rosco-m68k/rosco_m68k/code/firmware/attic/rhombus-monitor/README.md

# Machine-monitor from Rhombus 

This is the machine monitor from Rhombus (http://github.com/zenmetsu/rhombus) ported to run on the rosco_m68k.

Porting required fairly minimal effort (changes to the memory layout, changing the MFP initialisation to suit
my clocks and changing of a couple of address modes here and there due to the original being designed for
the 68020).

The main driving force behind porting this was as a sanity check while trying to debug the serial receiver.
I figured if this also didn't work then it would at least eliminate my own code as the reason the receiver
didn't work.

~It didn't (and as of today, doesn't) work. So it seems the problem is most likely a hardware issue.~ 
EDIT: Input is now working. The issue was found to be a faulty MC68901 IC - after replacing that it immediately worked. The monitor itself however does not work, instead it causes an illegal instruction on entry of any valid command. I suspect there is stll something MC68020-specific in here that VASM isn't picking up even with the -m68010 flag.

This code remains the property of it's original author(s) and is subject to the original license.
The original README is reproduced below in its entirity.

# rhombus

A minimal m68k system utilizing the 68020 microprocessor 

Project page located here: https://hackaday.io/project/8725-rhombus

Building upon the Motorola Application Note 1015 which can be found at the following address:
http://archive.retro.co.za/archive/computers/AppNotes/Motorola-AN1015.pdf

So far, there have been several typos which have been corrected within the original Motorola code, 
as well as one hardware fault in the included schematic.
As of https://github.com/zenmetsu/rhombus/commit/a4d3d180cdeede65c75aaab68ca234bd8a448fac   the code
is functional and will boot up to produce serial output.

The schematic within the application note is correct to the best of my knowledge with the exception
that on the MC68901, the TCO output must be tied externally to RC, and TDO needs to be tied to TC.
The provided schematic omitted these connections and the documentation for the multi-function peripheral
leaves much to be desired, leading one to suspect that the clock could be passed internally 
via configuration.

The system board currently consists of CPU, RAM, ROM, an MC68901 multifunction peripheral, and a Xilinx XC95108 CPLD.

RAM sizing and error checking is in place.  Monitor has the ability to analyze or change memory contents.
Secondary monitor written to expand functionality.  Register viewing/modification possible, as is vectored
selection of input/output devices.  Added NMI exception handler and trace/breakpoint functionality.

Second monitor now contains all of the functionality of the original.  I am currently attempting to migrate the system to a VME style bus, however I am debating using a standard VME bus with a non-standard 4x32 pin header.  The issue revolves around the feasibility of such a design due to the need for boards with more than 2 layers.

## Building

monitor.x68 can be assembled with vasm using the following command :

`vasmm68k_mot -m68020 -Fbin ./monitor.x68 -o monitor.bin`

The resulting binary can be loaded onto a ROM for booting.

## Additional programs
### mandelbrot - An ASCII Mandelbrot fractal explorer

mandelbrot.x68 can be assembled in the same manner as the monitor.  The resulting binary can be put into human readable format for pasting into the monitor with the following:

`xxd -u -s +15732736 -l 600 mandelbrot.bin | sed -e 's/  .*//' -e 's/^.*://' | sed -e :a -e '$!N; s/\n//; ta'`

Simply copy the code (including the leading space before the first long word) and, on the monitor, enter the command `MEM F01000`

After hitting Enter, paste the code and it should be placed into RAM.  When paste is done, hit Enter to exit memory write mode and execute the program with `JUMP F01000`

Keys are as follows:
```
W,A,S,D   PAN up/left/down/right
Q,E       ZOOM out/in
Z,C       ITERATION decrease,increase
R         RESETS to original conditions
X         EXITS to ROM monitor
```

## Next steps:

- S-Record load over serial
- Addition of an MC68681 DUART which will work as auxillary serial port as well as keyboard input
- Addition of FT245 USB FIFO for auxillary serial connection
- Increasing RAM data bus to 32bits.  ROM to remain 8bit due to simplicity of flashing devices.
- Floppy drive interface
- PS/2 Keyboard via intel N8042 microcontroller

Currently rebuilding CPLD files due to loss of CPLD project files
