rosco-m68k/rosco_m68k/code/software/lcd-ili9341/images/colorcube.bmp

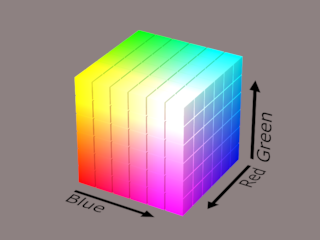
code/software/lcd-ili9341/images/colorcube.bmp
