rosco-m68k/rosco_m68k/code/software/lcd-ili9341/images/rosco_web.bmp

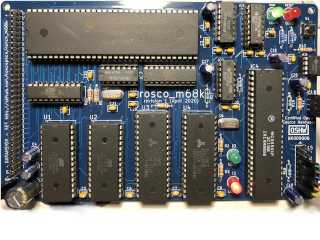
code/software/lcd-ili9341/images/rosco_web.bmp
