rosco-m68k/rosco_m68k/images/4077381582746008339.jpg

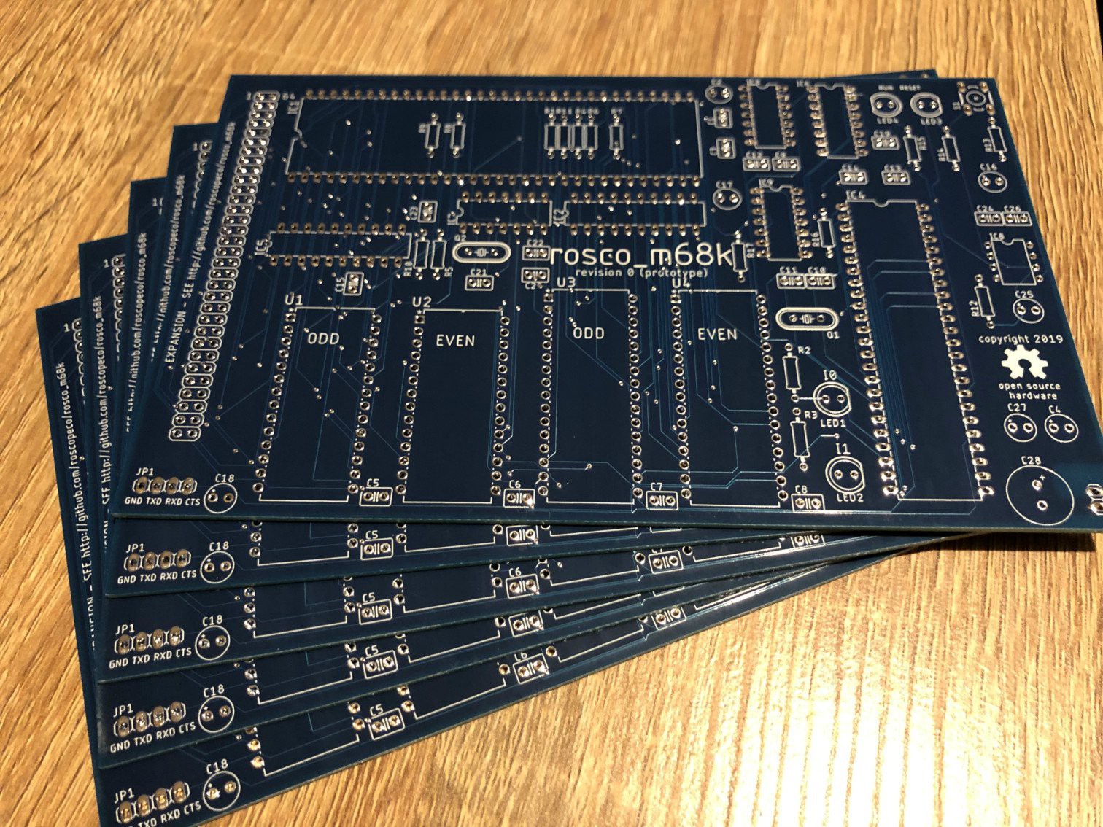
images/4077381582746008339.jpg
