rosco-m68k/rosco_m68k/images/bus_access_on_reset.png

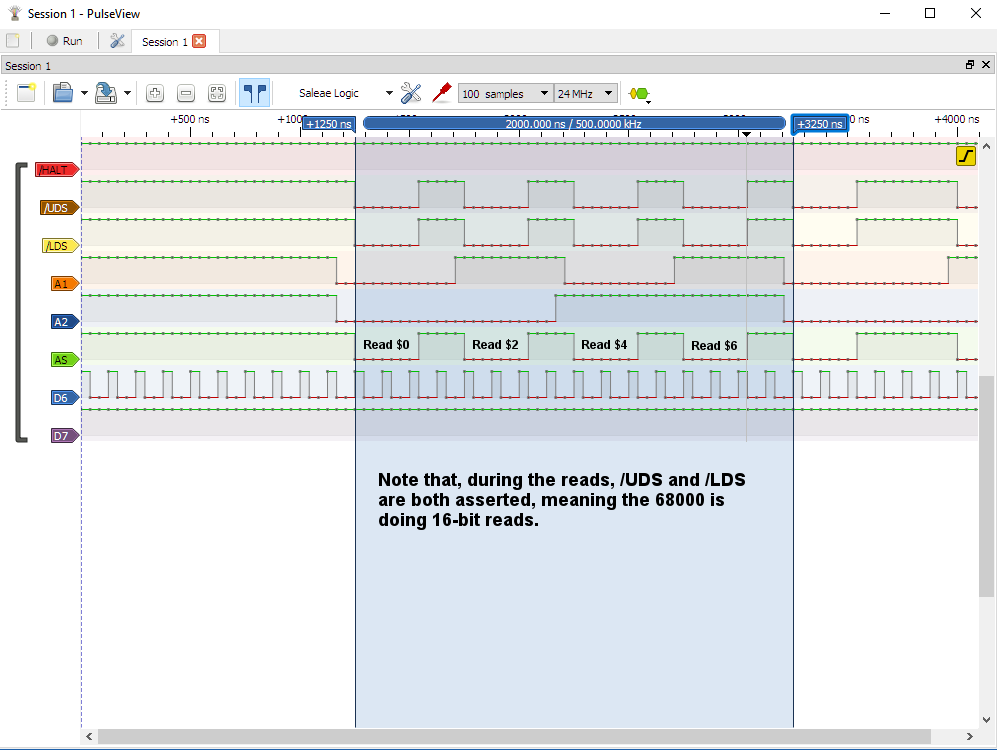
images/bus_access_on_reset.png
