rosco-m68k/rosco_m68k/images/pcb_r1.png

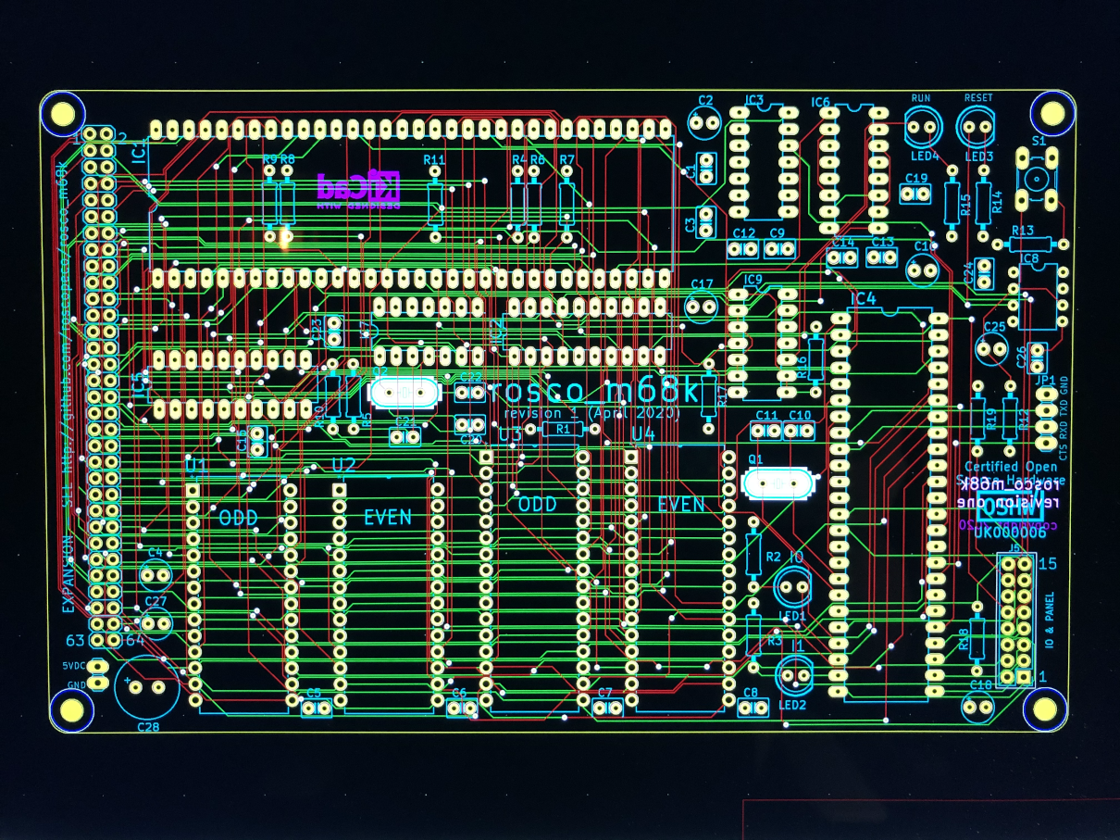
images/pcb_r1.png
