rosco-m68k/rosco_m68k/design/EAGLE/address_decoder_v2.sch

## EAGLE design design/EAGLE/address_decoder_v2.sch (2019-07-15)

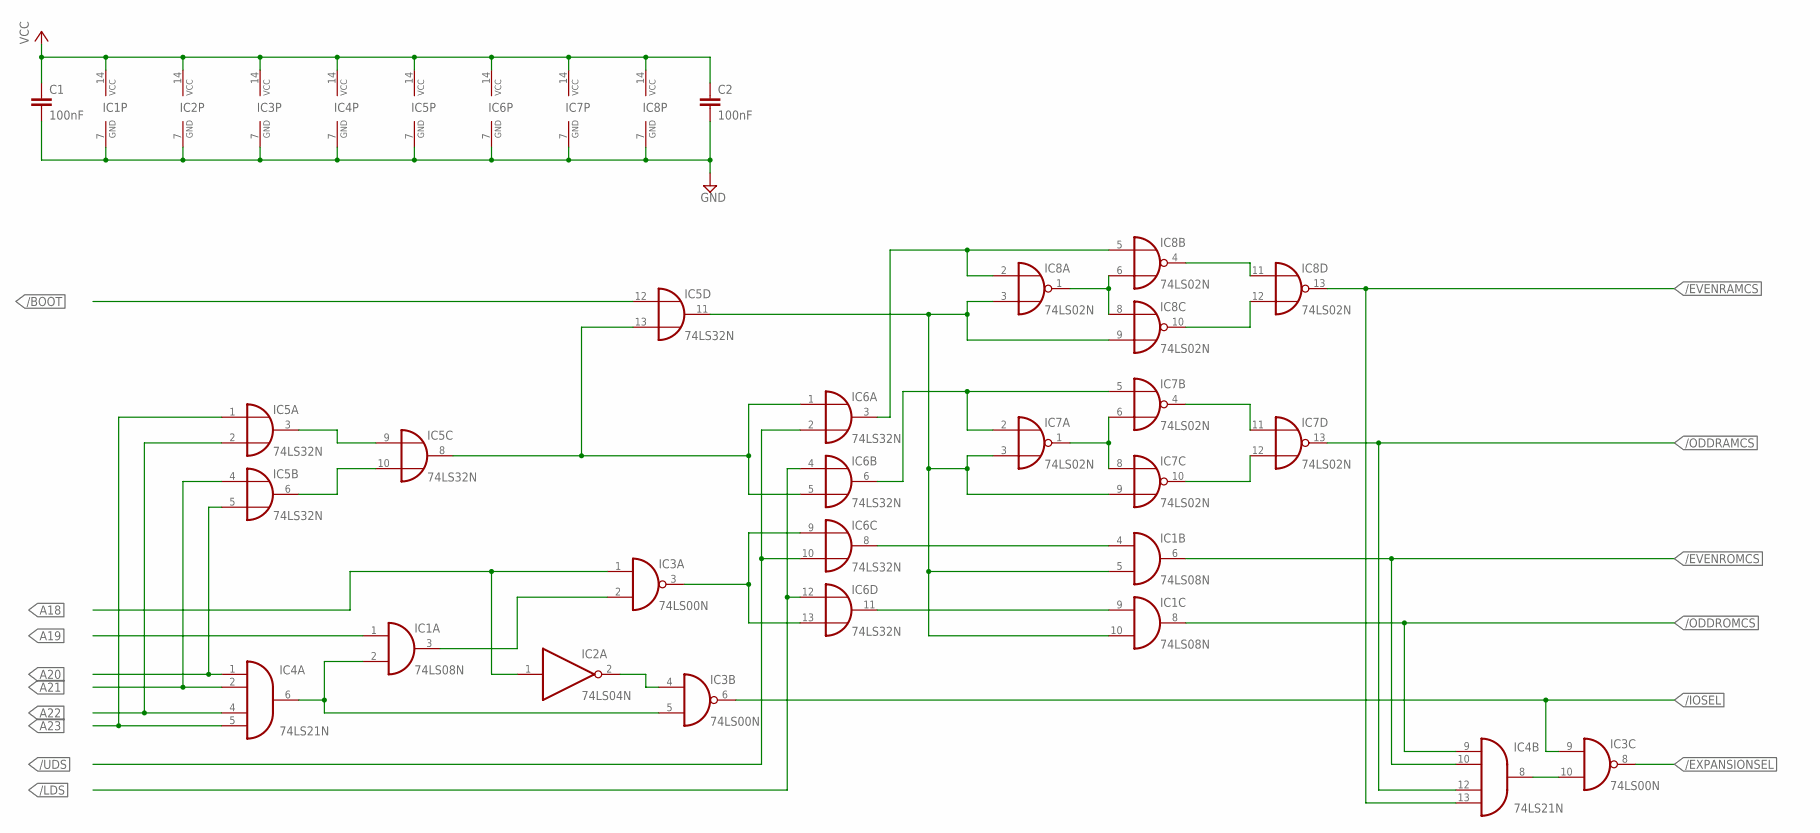
[picture p56: schematic address_decoder_v2.sch, sheet 1]

Parts:
C1, C2: 100nF; C025-024X044
IC1: 74LS08N; DIL14
IC2: 74LS04N; DIL14
IC3: 74LS00N; DIL14
IC4: 74LS21N; DIL14
IC5, IC6: 74LS32N; DIL14
IC7, IC8: 74LS02N; DIL14

Connections:
/BOOT: IC5.12 (I0)
/EVENRAMCS: IC4.13 (I3), IC8.13 (O)
/EVENROMCS: IC1.6 (O), IC4.10 (I1)
/EXPANSIONSEL: IC3.8 (O)
/IOSEL: IC3.6 (O), IC3.9 (I0)
/LDS: IC6.4 (I0), IC6.12 (I0)
/ODDRAMCS: IC4.12 (I2), IC7.13 (O)
/ODDROMCS: IC1.8 (O), IC4.9 (I0)
/UDS: IC6.2 (I1), IC6.10 (I1)
A18: IC2.1 (I), IC3.1 (I0)
A19: IC1.1 (I0)
A20: IC4.1 (I0), IC5.5 (I1)
A21: IC4.2 (I1), IC5.4 (I0)
A22: IC4.4 (I2), IC5.2 (I1)
A23: IC4.5 (I3), IC5.1 (I0)
GND: C1.2, C2.2, IC1.7 (GND), IC2.7 (GND), IC3.7 (GND), IC4.7 (GND), IC5.7 (GND), IC6.7 (GND), IC7.7 (GND), IC8.7 (GND)
unnamed: IC8.1 (O), IC8.6 (I1), IC8.8 (I0)
unnamed: IC8.4 (O), IC8.11 (I0)
unnamed: IC8.10 (O), IC8.12 (I1)
unnamed: IC6.3 (O), IC8.2 (I0), IC8.5 (I0)
unnamed: IC3.10 (I1), IC4.8 (O)
unnamed: IC7.1 (O), IC7.6 (I1), IC7.8 (I0)
unnamed: IC7.4 (O), IC7.11 (I0)
unnamed: IC6.6 (O), IC7.2 (I0), IC7.5 (I0)
unnamed: IC1.5 (I1), IC1.10 (I1), IC5.11 (O), IC7.3 (I1), IC7.9 (I1), IC8.3 (I1), IC8.9 (I1)
unnamed: IC7.10 (O), IC7.12 (I1)
unnamed: IC1.4 (I0), IC6.8 (O)
unnamed: IC1.9 (I0), IC6.11 (O)
unnamed: IC5.3 (O), IC5.9 (I0)
unnamed: IC5.6 (O), IC5.10 (I1)
unnamed: IC3.3 (O), IC6.9 (I0), IC6.13 (I1)
unnamed: IC1.2 (I1), IC3.5 (I1), IC4.6 (O)
unnamed: IC2.2 (O), IC3.4 (I0)
unnamed: IC5.8 (O), IC5.13 (I1), IC6.1 (I0), IC6.5 (I1)
unnamed: IC1.3 (O), IC3.2 (I1)
VCC: C1.1, C2.1, IC1.14 (VCC), IC2.14 (VCC), IC3.14 (VCC), IC4.14 (VCC), IC5.14 (VCC), IC6.14 (VCC), IC7.14 (VCC), IC8.14 (VCC)

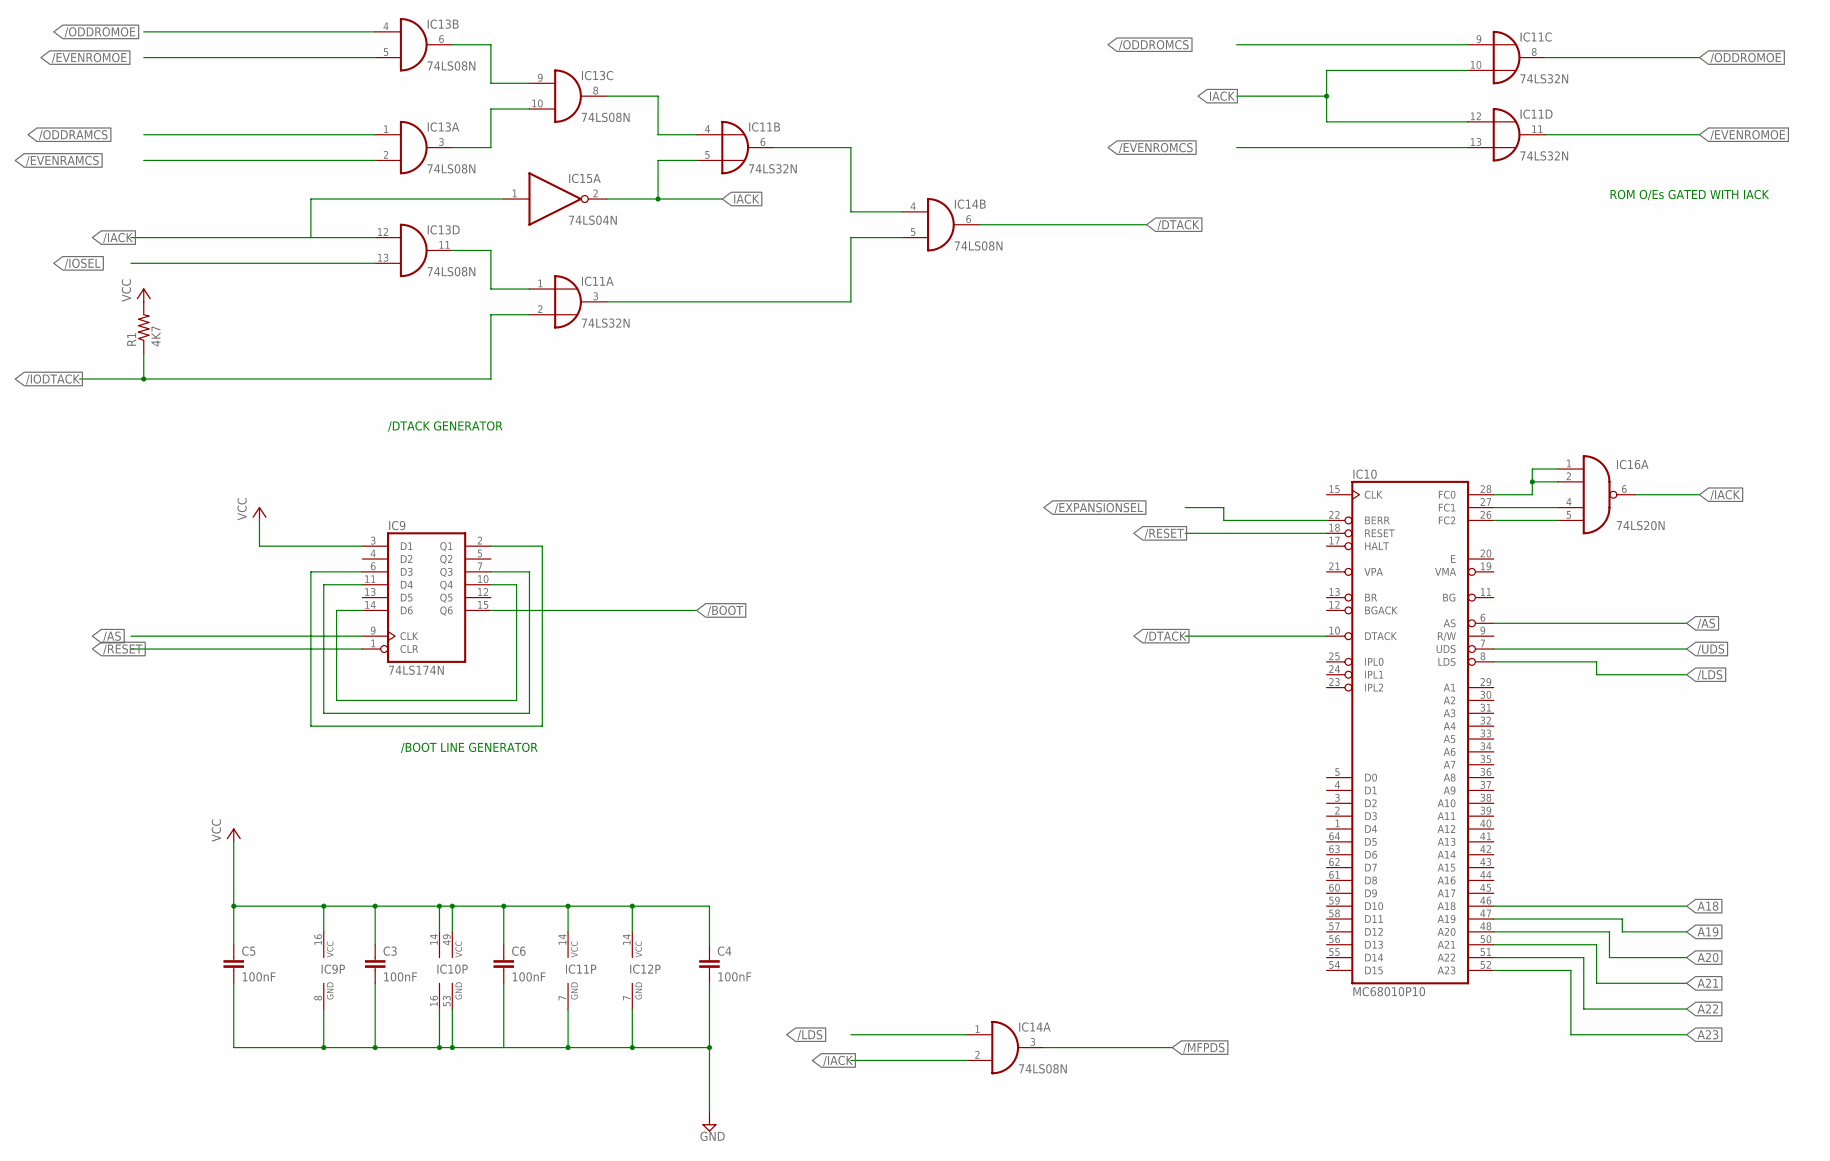
[picture p57: schematic address_decoder_v2.sch, sheet 2]

Parts:
C3, C4, C5, C6: 100nF; C5B3
IC9: 74LS174N; DIL16
IC10: MC68010P10; DIL64
IC11: 74LS32N; DIL14
IC12: 74LS21N; DIL14
IC13, IC14: 74LS08N; DIL14
IC15: 74LS04N; DIL14
IC16: 74LS20N; DIL14
R1: 4K7; 0204/7

Connections:
/AS: IC9.9 (CLK), IC10.6 (AS)
/BOOT: IC9.15 (Q6)
/DTACK: IC10.10 (DTACK), IC14.6 (O)
/EVENRAMCS: IC13.2 (I1)
/EVENROMCS: IC11.13 (I1)
/EVENROMOE: IC11.11 (O), IC13.5 (I1)
/EXPANSIONSEL: IC10.22 (BERR)
/IACK: IC13.12 (I0), IC14.2 (I1), IC15.1 (I), IC16.6 (O)
/IODTACK: IC11.2 (I1), R1.1
/IOSEL: IC13.13 (I1)
/LDS: IC10.8 (LDS), IC14.1 (I0)
/MFPDS: IC14.3 (O)
/ODDRAMCS: IC13.1 (I0)
/ODDROMCS: IC11.9 (I0)
/ODDROMOE: IC11.8 (O), IC13.4 (I0)
/RESET: IC9.1 (CLR), IC10.18 (RESET)
/UDS: IC10.7 (UDS)
A18: IC10.46 (A18)
A19: IC10.47 (A19)
A20: IC10.48 (A20)
A21: IC10.50 (A21)
A22: IC10.51 (A22)
A23: IC10.52 (A23)
GND: C3.2, C4.2, C5.2, IC9.8 (GND), IC10.16 (GND), IC10.53 (GND), IC11.7 (GND), IC12.7 (GND)
GND1: C6.2
IACK: IC11.5 (I1), IC11.10 (I1), IC11.12 (I0), IC15.2 (O)
unnamed: IC13.6 (O), IC13.9 (I0)
unnamed: IC9.7 (Q3), IC9.11 (D4)
unnamed: IC9.10 (Q4), IC9.14 (D6)
unnamed: IC9.2 (Q1), IC9.6 (D3)
unnamed: IC13.3 (O), IC13.10 (I1)
unnamed: IC11.4 (I0), IC13.8 (O)
unnamed: IC11.1 (I0), IC13.11 (O)
unnamed: IC11.6 (O), IC14.4 (I0)
unnamed: IC11.3 (O), IC14.5 (I1)
unnamed: IC10.26 (FC2), IC16.5 (I3)
unnamed: IC10.27 (FC1), IC16.4 (I2)
unnamed: IC10.28 (FC0), IC16.1 (I0), IC16.2 (I1)
VCC: C3.1, C4.1, C5.1, C6.1, IC9.3 (D1), IC9.16 (VCC), IC10.14 (VCC), IC10.49 (VCC), IC11.14 (VCC), IC12.14 (VCC), R1.2

Notes on the sheet:
/BOOT LINE GENERATOR
/DTACK GENERATOR
ROM O/Es GATED WITH IACK
