rosco-m68k/rosco_m68k/design/EAGLE/clock.sch

## EAGLE design design/EAGLE/clock.sch (2019-03-28)

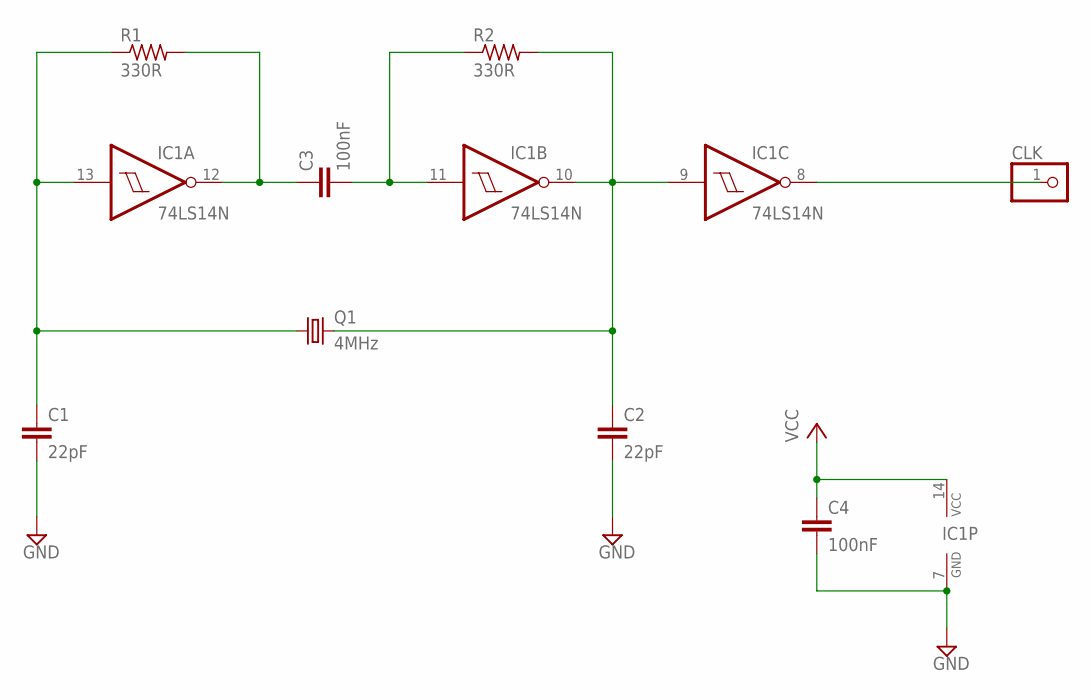
[picture p59: schematic clock.sch]

Parts:
C1, C2: 22pF; C025-025X050
C3, C4: 100nF; C025-025X050
CLK: PINHD-1X1; 1X01
IC1: 74LS14N; DIL14
Q1: 4MHz; HC49/S
R1, R2: 330R; 0207/10

Connections:
GND: C1.2, C2.2, C4.2, IC1.7 (GND)
unnamed: C3.1, IC1.12 (O), R1.2
unnamed: C3.2, IC1.11 (I), R2.1
unnamed: C2.1, IC1.9 (I), IC1.10 (O), Q1.2, R2.2
unnamed: C1.1, IC1.13 (I), Q1.1, R1.1
unnamed: CLK.1, IC1.8 (O)
VCC: C4.1, IC1.14 (VCC)
