rosco-m68k/rosco_m68k/design/EAGLE/dtack-generator.sch

## EAGLE design design/EAGLE/dtack-generator.sch (2019-05-19)

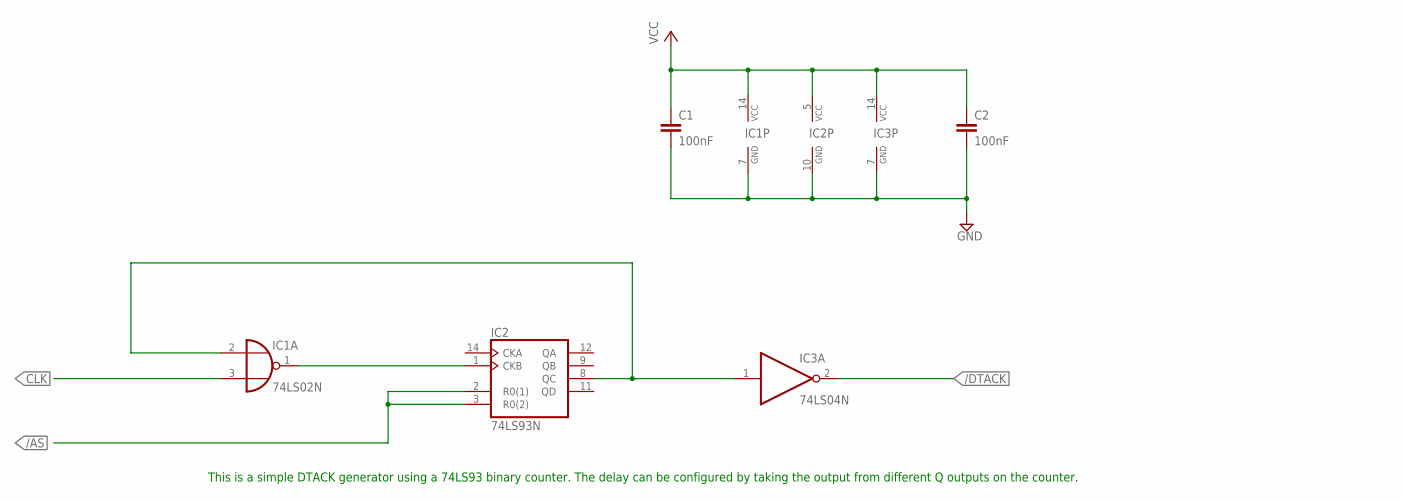
[picture p60: schematic dtack-generator.sch]

Parts:
C1, C2: 100nF; C025-024X044
IC1: 74LS02N; DIL14
IC2: 74LS93N; DIL14
IC3: 74LS04N; DIL14

Connections:
/AS: IC2.2 (R0(1)), IC2.3 (R0(2))
/DTACK: IC3.2 (O)
CLK: IC1.3 (I1)
GND: C1.2, C2.2, IC1.7 (GND), IC2.10 (GND), IC3.7 (GND)
unnamed: IC1.1 (O), IC2.1 (CKB)
unnamed: IC1.2 (I0), IC2.8 (QC), IC3.1 (I)
VCC: C1.1, C2.1, IC1.14 (VCC), IC2.5 (VCC), IC3.14 (VCC)

Notes on the sheet:
This is a simple DTACK generator using a 74LS93 binary counter. The delay can be configured by taking the output from different Q outputs on the counter.
