rosco-m68k/rosco_m68k/design/EAGLE/m68k_free_run.sch

## EAGLE design design/EAGLE/m68k_free_run.sch (2019-04-28)

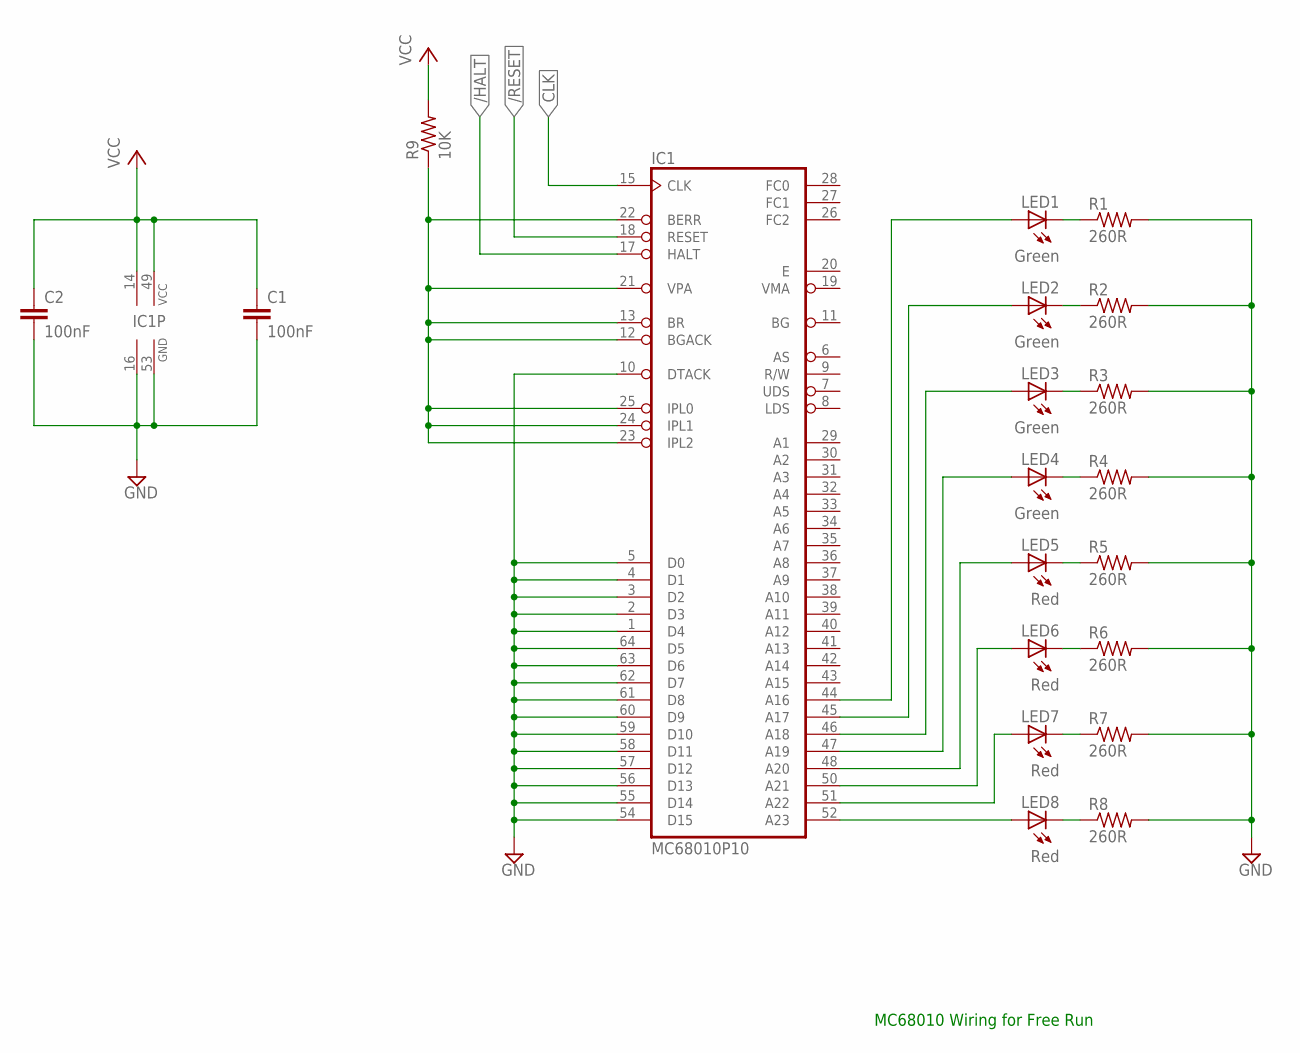
[picture p61: schematic m68k_free_run.sch]

Parts:
C1, C2: 100nF; C025-024X044
IC1: MC68010P10; DIL64
LED1, LED2, LED3, LED4: Green; LED5MM
LED5, LED6, LED7, LED8: Red; LED5MM
R1, R2, R3, R4, R5, R6, R7, R8: 260R; 0207/10
R9: 10K; 0207/10

Connections:
/HALT: IC1.17 (HALT)
/RESET: IC1.18 (RESET)
CLK: IC1.15 (CLK)
GND: C1.2, C2.2, IC1.1 (D4), IC1.2 (D3), IC1.3 (D2), IC1.4 (D1), IC1.5 (D0), IC1.10 (DTACK), IC1.16 (GND), IC1.53 (GND), IC1.54 (D15), IC1.55 (D14), IC1.56 (D13), IC1.57 (D12), IC1.58 (D11), IC1.59 (D10), IC1.60 (D9), IC1.61 (D8), IC1.62 (D7), IC1.63 (D6), IC1.64 (D5), R1.2, R2.2, R3.2, R4.2, R5.2, R6.2, R7.2, R8.2
unnamed: IC1.52 (A23), LED8.A
unnamed: IC1.51 (A22), LED7.A
unnamed: IC1.50 (A21), LED6.A
unnamed: IC1.48 (A20), LED5.A
unnamed: IC1.47 (A19), LED4.A
unnamed: IC1.46 (A18), LED3.A
unnamed: IC1.45 (A17), LED2.A
unnamed: IC1.44 (A16), LED1.A
unnamed: LED1.K (C), R1.1
unnamed: LED2.K (C), R2.1
unnamed: LED3.K (C), R3.1
unnamed: LED4.K (C), R4.1
unnamed: LED5.K (C), R5.1
unnamed: LED6.K (C), R6.1
unnamed: LED7.K (C), R7.1
unnamed: LED8.K (C), R8.1
unnamed: IC1.12 (BGACK), IC1.13 (BR), IC1.21 (VPA), IC1.22 (BERR), IC1.23 (IPL2), IC1.24 (IPL1), IC1.25 (IPL0), R9.1
VCC: C1.1, C2.1, IC1.14 (VCC), IC1.49 (VCC), R9.2

Notes on the sheet:
MC68010 Wiring for Free Run
