rosco-m68k/rosco_m68k/design/EAGLE/reset_circuit.sch

## EAGLE design design/EAGLE/reset_circuit.sch (2019-06-25)

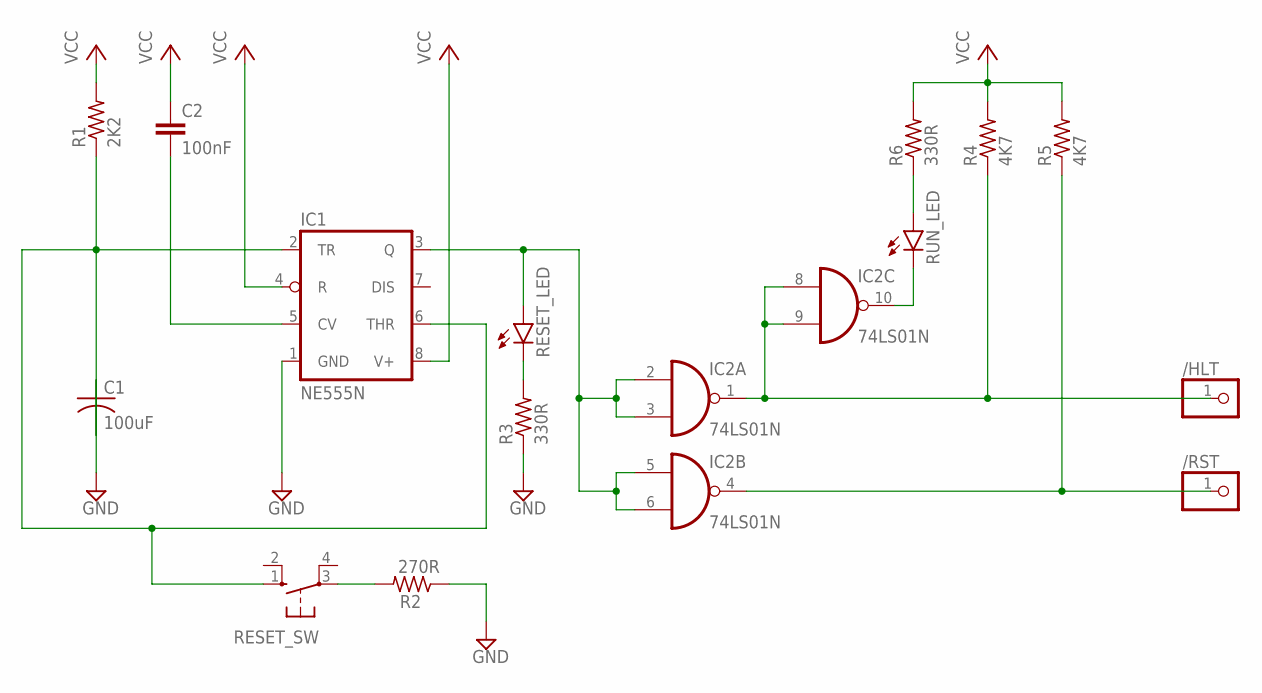
[picture p62: schematic reset_circuit.sch]

Parts:
/HLT: PINHD-1X1; 1X01
/RST: PINHD-1X1; 1X01
C1: 100uF; C025-025X050
C2: 100nF; C2.5-3
IC1: NE555N; DIL08
IC2: 74LS01N; DIL14
R1: 2K2; 0204/7
R2: 270R; 0204/7
R3, R6: 330R; 0204/7
R4, R5: 4K7; 0204/7
RESET_LED: LED5MM
RESET_SW: 10-XX; B3F-10XX
RUN_LED: LED5MM

Connections:
GND: C1.1, IC1.1 (GND), R2.1, R3.1
unnamed: C1.2, IC1.2 (TR), IC1.6 (THR), R1.1, RESET_SW.1 (S)
unnamed: C2.2, IC1.5 (CV)
unnamed: IC1.3 (Q), IC2.2 (I0), IC2.3 (I1), IC2.5 (I0), IC2.6 (I1), RESET_LED.A
unnamed: R3.2, RESET_LED.K (C)
unnamed: /HLT.1, IC2.1 (O), IC2.8 (I0), IC2.9 (I1), R4.1
unnamed: /RST.1, IC2.4 (O), R5.1
unnamed: IC2.10 (O), RUN_LED.K (C)
unnamed: R6.1, RUN_LED.A
unnamed: R2.2, RESET_SW.3
VCC: C2.1, IC1.4 (R), IC1.8 (V+), R1.2, R4.2, R5.2, R6.2
