rosco-m68k/rosco_m68k/design/r1.2/kicad/Cpu_Ram_Rom.sch

## KiCad design design/r1.2/kicad/Cpu_Ram_Rom.sch (2021-04-14)

Schematic: Cpu_Ram_Rom.sch

Parts:
C1, C2: 33pF; C2.5-3
C5, C6, C7, C8: 100nF; C2.5-3
IC1: MC68010P10; DIL64
IC4: MC68901P; DIL48
J2: Conn_01x06; 1X06
JP1: FTDI POWER; 1X02
LED1: GREEN; LED5MM
LED2: RED; LED5MM
Q1: 3.6864MHz; HC49_S
R1, R2: 330R; 0207_10
U1, U2: AT28C256-15PU; DIP-28_W15.24mm_LongPads
U3, U4: AS6C4008-55PCN; DIP-32_W15.24mm_LongPads

Notes on the sheet:
ODD
EVEN
MC68901
MC68010P10
AT28C64B or AT28C256
