rosco-m68k/rosco_m68k/design/r1.2/kicad/Glue.sch

## KiCad design design/r1.2/kicad/Glue.sch (2021-04-14)

Schematic: Glue.sch

Parts:
C7, C8, C9, C12, C13, C26: 100nF; C2.5-3
C25: 100uF; E2,5-5
IC2, IC3, IC5: ATF16V8BQL-15PU; DIL20
IC6: 74174N; DIP-16_W7.62mm_Socket_LongPads
IC7: 74LS93; DIP-14_W7.62mm_Socket_LongPads
IC8: 555N; DIP-8_W7.62mm_LongPads
IC9: 74LS01N; DIP-14_W7.62mm_Socket_LongPads
LED3: RED; LED5MM
LED4: GREEN; LED5MM
Q2: 5H8ET-10.000; Oscillator_DIP-8
Q3: 5H8ET-4.000; Oscillator_DIP-8
R3, R4, R6, R7, R8, R9, R11, R16, R17: 4K7; 0207_10
R12, R21: 2K2; 0207_10
R13: 270R; 0207_10
R14, R15: 330R; 0207_10
S1: 10-XX; B3F-10XX

Notes on the sheet:
RESET CIRCUIT
GLUE_LOGIC.PLD
/BOOT LINE GENERATOR
ADDRESS_DECODER.PLD
MFPSEL.PLD
DTACK WATCHDOG
