rosco-m68k/rosco_m68k/design/r1/kicad/Clock_Reset.sch

## KiCad design design/r1/kicad/Clock_Reset.sch (2020-05-26)

Schematic: Clock_Reset.sch

Parts:
C20, C22: 22pF; C2.5-3
C21, C23, C24, C26: 100nF; C2.5-3
C25, C27: 100uF; E2,5-5
C28: 470uF; E3,5-10
IC7: 7404N; DIL14
IC8: 555N; DIL08
IC9: 74LS01N; DIL14
JP2: PWR; 1X02
LED3: RED; LED5MM
LED4: GREEN; LED5MM
Q2: 8MHz; HC49_S
R4, R6, R7, R8, R9, R11, R16, R17: 4K7; 0207_10
R5, R10, R15: 1K2; 0207_10
R12: 2K2; 0207_10
R13: 270R; 0207_10
R14: 330R; 0207_10
S1: 10-XX; B3F-10XX

Notes on the sheet:
RESET CIRCUIT
SYSTEM CLOCK CIRCUIT
