rosco-m68k/rosco_m68k/design/r1/kicad/Dtack_Boot.sch

## KiCad design design/r1/kicad/Dtack_Boot.sch (2020-03-29)

Schematic: Dtack_Boot.sch

Parts:
C15, C19: 100nF; C2.5-3
C16, C17, C18: 100uF; E2,5-5
IC5: ATF16V8BQL; DIL20
IC6: 74174N; DIL16

Notes on the sheet:
/BOOT LINE GENERATOR
GLUE_LOGIC.PLD
