rosco-m68k/rosco_m68k/design/r1/kicad/MC68901_Decoder.sch

## KiCad design design/r1/kicad/MC68901_Decoder.sch (2020-05-25)

Schematic: MC68901_Decoder.sch

Parts:
C9, C12, C13, C14: 100nF; C2.5-3
C10, C11: 33pF; C2.5-3
IC2: ATF16V8BQL-15PU; DIL20
IC3: 7493N; DIL14
IC4: MC68901P; DIL48
JP1: UART; 1X04
LED1: GREEN; LED5MM
LED2: RED; LED5MM
Q1: 3.6864MHz; HC49_S
R2: 1K2; 0207_10
R3: 330R; 0207_10

Notes on the sheet:
MC68901
ADDRESS_DECODER.PLD
