rosco-m68k/rosco_m68k/code/software/gpiodemo/example-circuit/circuit.sch

## KiCad design code/software/gpiodemo/example-circuit/circuit.sch (2020-03-31)

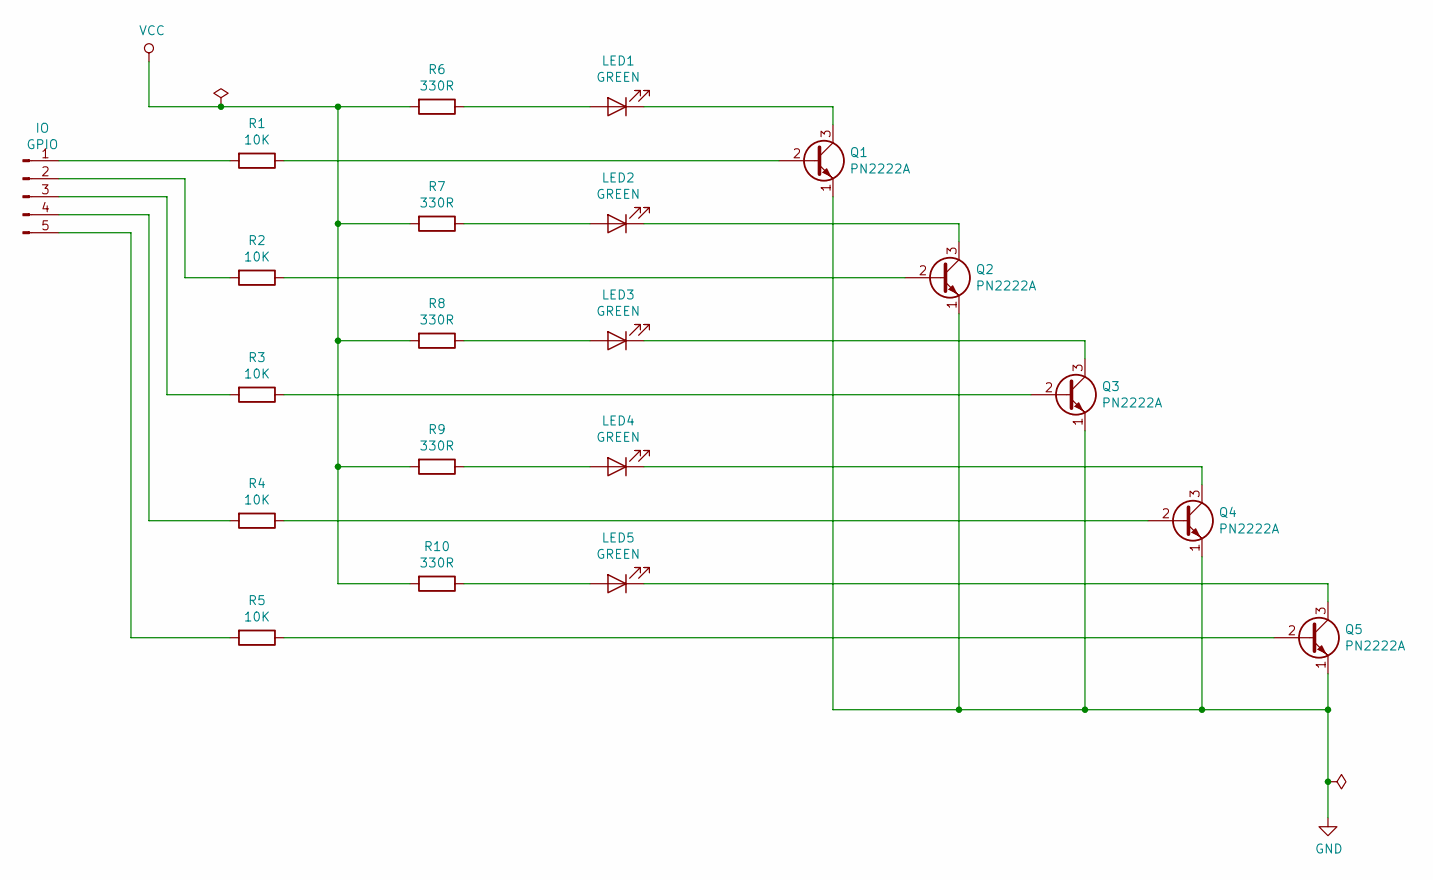
[picture p63: schematic circuit.sch]

Parts:
IO: GPIO
LED1, LED2, LED3, LED4, LED5: GREEN
Q1, Q2, Q3, Q4, Q5: PN2222A; TO-92_Inline
R1, R2, R3, R4, R5: 10K
R6, R7, R8, R9, R10: 330R

Connections:
GND: Q1.1 (E), Q2.1 (E), Q3.1 (E), Q4.1 (E), Q5.1 (E), R6.2, R7.2, R8.2, R9.2, R10.2
unnamed: IO.1, R1.2
unnamed: IO.2, R2.2
unnamed: IO.3, R3.2
unnamed: IO.4, R4.2
unnamed: IO.5, R5.2
unnamed: LED1.1 (K), Q1.3 (C)
unnamed: LED1.2 (A), R6.1
unnamed: LED2.1 (K), Q2.3 (C)
unnamed: LED2.2 (A), R7.1
unnamed: LED3.1 (K), Q3.3 (C)
unnamed: LED3.2 (A), R8.1
unnamed: LED4.1 (K), Q4.3 (C)
unnamed: LED4.2 (A), R9.1
unnamed: LED5.1 (K), Q5.3 (C)
unnamed: LED5.2 (A), R10.1
unnamed: Q1.2 (B), R1.1
unnamed: Q2.2 (B), R2.1
unnamed: Q3.2 (B), R3.1
unnamed: Q4.2 (B), R4.1
unnamed: Q5.2 (B), R5.1
