rosco-m68k/rosco_m68k/code/software/gpio-interrupt/gpio-interrupt.c

/*
 * vim: set et ts=4 sw=4
 *------------------------------------------------------------
 *                                  ___ ___ _
 *  ___ ___ ___ ___ ___       _____|  _| . | |_
 * |  _| . |_ -|  _| . |     |     | . | . | '_|
 * |_| |___|___|___|___|_____|_|_|_|___|___|_,_|
 *                     |_____|
 * ------------------------------------------------------------
 * Copyright (c) 2020 Xark
 * MIT License
 * ------------------------------------------------------------
 */

#include <basicio.h>
#include <gpio.h>
#include <machine.h>

// macro for easier MFP register access (read or write)
#define MFP(reg) (*(volatile uint8_t *)MFP_##reg)

// Bit 6 in IREB, IPRB and ISRB corresponds to rosco GPIO3
// See page 3-4 in 1984 MC68901 MFP pdf
#define MFP_GPIP4_BIT 0x40

void (*prev_handler)();               // previous interupt handler address
volatile int gpio3_interrupts;        // counter for number of GPIO3 interrupts

// GPIO3 interrupt handler.  The "interrupt" attribute "tells the compiler to
// save all the registers in this function and use the "rte" return from
// exception instruction at the end instead of the normal "rts" return from
// subroutine instruction.  This allows the interrupt handler to be written in
// C.
void gpio3_handler(void) __attribute__((interrupt));
void gpio3_handler(void)
{
    MFP(GPDR) ^= 2;                    // toggle red LED
    gpio3_interrupts += 1;             // increment interrupt counter
    print("<Interrupted!>");           // "interrupt" main printing
    MFP(ISRB) = ~MFP_GPIP4_BIT;        // clear interrupt in-service bit
}

int main(int argc, char ** argv)
{
    (void)argc;
    (void)argv;

    println("");
    println("*** MFP GPIO Interrupt Test ***");
    println("          by Xark");
    println("(built on " __DATE__ " at " __TIME__ ")");
    println("");
    print("rosco_m68k firmware version: ");
    printushort(_FIRMWARE_REV >> 16);
    print(".");
    printuchar(_FIRMWARE_REV >> 8);
    print(".");
    printuchar(_FIRMWARE_REV);
    println("");
    println("This will test interrupt generation on a negative");
    println("edge on rosco GPIO3 (J5-pin 5 aka MFP GPIP4).");

    println("Initializing MFP for GPIP4 interrupt...");

    // It is documented that if you are "unlucky" and touch the MFP interrupt
    // registers at "just the wrong time" (as another interrupt happens etc.)
    // the MFP can generate a "spurious interrupt" (which will lead to red LED
    // blinking, and sadness).  So we disable all interrupts for the short
    // period while we set the MFP interrupt registers (and re-enable them right
    // after).
    uint8_t intr_mask = mcDisableInterrupts();

    // NOTE: These use the normal GPIO bit values (from gpio.h)
    MFP(DDR) &= ~GPIO3;         // clear GPIO3 data direction for input (0=in, 1=out)
    MFP(GPDR) &= ~GPIO3;        // clear GPIO3 data register (likely not necessary)
    MFP(AER) &= ~GPIO3;         // set GPIO3 active edge to falling (0=falling, 1=rising)

    // NOTE: Since these are spread between two 8-bit registers, they use a different
    //       bit than the GPIO definition.  See page 3-4 in 1984 MC68901 MFP pdf
    MFP(IERB) |= MFP_GPIP4_BIT;        // set MFP GPIP4 interrupt enable
    MFP(IPRB) = ~MFP_GPIP4_BIT;        // clear MFP GPIP4 interrupt pending
    MFP(ISRB) = ~MFP_GPIP4_BIT;        // clear interrupt in-service bit
    MFP(IMRB) |= MFP_GPIP4_BIT;        // set interrupt enable mask bit

    // Set MFP GPIP4 interrupt handler vector.  The rosco linker scripts provides
    // the _MFP_VECTORS symbol for the 16 MFP interrupt vectors (vector #64 at
    // address 0x100, the user-interrupt vector where rosco directs MFP
    // interrupts).  Since GPIP4 is MFP interrupt source #6 (see page 3-1 in
    // 1984 MC68901 MFP pdf) set the the 6th element with the address of the
    // interrupt handler
    prev_handler    = _MFP_VECTORS[6];        // save old handler (to restore on exit)
    _MFP_VECTORS[6] = gpio3_handler;          // set new GPIP4 interrupt handler

    mcEnableInterrupts(intr_mask);        // re-enable interrupts

    println("Done.  Now ready for a GPIO3 interrupt.");
    println("");
    println("Mainline will keep loop_counting, waiting for interrupts.");
    println("");
    println("Press any key to exit.");
    println("");

    int loop_count = 0;
    do
    {
        print("loop #=");
        printuint(loop_count);
        print(" GPIO3 interrupts=");
        printuint(gpio3_interrupts);
        print(" 100Hz timer=");
        printuint(_TIMER_100HZ);
        println("...");

        mcDelaymsec10(100);        // delay for 1 second

        loop_count++;

    } while (!(MFP(RSR) & 0x80));        // loop until a char is waiting in UART buffer

    // disable GPIO interrupts
    MFP(IERB) &= ~MFP_GPIP4_BIT;        // clear MFP GPIP4 interrupt enable
    MFP(IMRB) &= ~MFP_GPIP4_BIT;        // clear interrupt enable mask bit

    // restore previous interrupt handler
    _MFP_VECTORS[6] = prev_handler;

    println("");
    println("Glad to be of service!");        // invoke Genuine Rosco Personality(TM) module

    return 0;
}
