rosco-m68k/rosco_m68k/code/firmware/rosco_m68k_development/stage2/sdfat/bbsd.c

/*
 *------------------------------------------------------------
 *                                  ___ ___ _
 *  ___ ___ ___ ___ ___       _____|  _| . | |_
 * |  _| . |_ -|  _| . |     |     | . | . | '_|
 * |_| |___|___|___|___|_____|_|_|_|___|___|_,_|
 *                     |_____|       firmware v1
 * ------------------------------------------------------------
 * Copyright (c)2020 Ross Bamford
 * See top-level LICENSE.md for licence information.
 *
 * rosco_m68k Bit-Banged SD Card over SPI
 * ------------------------------------------------------------
 */

#include <stdbool.h>
#include <stdint.h>

#include "bbspi.h"
#include "bbsd.h"
#include "device/block.h"

// Will try to idle the SD this many times before giving up
#define MAX_IDLE_TRIES    5

static bool wait_for_card(BBSPI*, uint32_t);
static void reset_card(BBSPI*);
static bool wait_for_block_start(BBSPI*, uint32_t);
static bool send_idle(BBSPI*);
static BBSDCardType get_card_type(BBSPI*);
static bool try_acmd41(BBSPI*, uint32_t, uint32_t);
static uint8_t raw_sd_command(BBSPI*, uint8_t, uint32_t);
static uint8_t raw_sd_acommand(BBSPI*, uint8_t, uint32_t);
static bool sd_partial_read_p(BBSDCard *sd);

// BlockDevice handlers
static uint32_t sd_device_block_size_func(BlockDevice *device);
static bool sd_device_read_block_func(BlockDevice *device, uint32_t block, void *buffer);
static bool sd_device_read_func(BlockDevice *device, uint32_t block, uint32_t start_ofs, uint32_t len, void *buffer);
static bool sd_device_write_func(BlockDevice *device, uint32_t block, uint32_t start_ofs, uint32_t len, void *buffer);

bool BBSD_initialize(BBSDCard *sd, BBSPI *spi) {
#ifndef SD_FASTER
#ifdef SPI_FASTER
    if (sd->initialized) {
#else
    if (sd->initialized || !spi->initialized) {
#endif
        return false;
    }
#endif

    bool result = false;

    reset_card(spi);

    if (!send_idle(spi)) {
        goto finally;
    }

    BBSDCardType card_type = get_card_type(spi);

    if (card_type == BBSD_CARD_TYPE_UNKNOWN) {
        goto finally;
    }

    // Try to initialize the card...
    uint32_t supports = card_type == BBSD_CARD_TYPE_V2 ? 0x40000000 : 0;

    if (try_acmd41(spi, 100, supports)) {
        if (card_type == BBSD_CARD_TYPE_V2) {
            // check OCR for SDHC...
            if (raw_sd_command(spi, 58, 0)) {
                goto finally;
            } else {
                if (BBSPI_recv_byte(spi) & 0xC0) {
                    card_type = BBSD_CARD_TYPE_SDHC;

                    // don't care about voltage range...
                    BBSPI_recv_byte(spi);
                    BBSPI_recv_byte(spi);
                    BBSPI_recv_byte(spi);

                    sd->type = card_type;
                    sd->spi = spi;

#ifndef SD_BLOCK_READ_ONLY
                    sd->have_current_block = false;

                    // TODO this can't currently signal error!
                    sd->can_partial_read = sd_partial_read_p(sd);
#endif

#ifndef SD_FASTER
                    sd->initialized = true;
#endif

                    result = true;
                }
            }
        }
    }

finally:
    BBSPI_deassert_cs(spi);
    return result;
}


bool BBSD_make_device(BBSDCard *sd, BlockDevice *device) {
#ifndef SD_FASTER
    if (device->initialized) {
        return false;
    }
#endif

    device->initialized = true;
    device->getBlockSize = sd_device_block_size_func;
    device->readBlock = sd_device_read_block_func;
    device->read = sd_device_read_func;
    device->write = sd_device_write_func;
    device->device_data = sd;

    return true;
}


uint8_t BBSD_command(BBSDCard *sd, uint8_t command, uint32_t arg) {
#ifndef SD_FASTER
    if (sd->initialized) {
#endif
        return raw_sd_command(sd->spi, command, arg);
#ifndef SD_FASTER
    } else {
        return 0xFF;
    }
#endif
}

uint8_t BBSD_acommand(BBSDCard *sd, uint8_t command, uint32_t arg) {
#ifndef SD_FASTER
    if (sd->initialized) {
#endif
        return raw_sd_acommand(sd->spi, command, arg);
#ifndef SD_FASTER
    } else {
        return 0xFF;
    }
#endif
}

#ifndef SD_MINIMAL
bool BBSD_readreg(BBSDCard *sd, uint8_t command, uint8_t *buf) {
#ifndef SD_FASTER
    if (!sd->initialized) {
        return false;
    }
#endif

    bool result = false;

    if (!raw_sd_command(sd->spi, command, 0)) {
        if (wait_for_block_start(sd->spi, 10)) {
            for (uint32_t i = 0; i < 16; i++) {
                buf[i] = BBSPI_recv_byte(sd->spi);
            }

            // Ignore CRCs...
            BBSPI_recv_byte(sd->spi);
            BBSPI_recv_byte(sd->spi);

            result = true;
        }
    }

    BBSPI_deassert_cs(sd->spi);
    return result;
}

bool BBSD_get_csd(BBSDCard *sd, BBSDCard_CSD *csd) {
    return BBSD_readreg(sd, 9, (uint8_t*) csd);
}

static BBSDCard_CSD csdbuf;

uint32_t BBSD_get_size(BBSDCard *sd) {
    if (!BBSD_get_csd(sd, &csdbuf)) {
        return 0;
    }
    if (csdbuf.v1.csd_ver == 0) {
        uint8_t read_bl_len = csdbuf.v1.read_bl_len;
        uint16_t c_size = (csdbuf.v1.c_size_high << 10)
                | (csdbuf.v1.c_size_mid << 2) | csdbuf.v1.c_size_low;
        uint8_t c_size_mult = (csdbuf.v1.c_size_mult_high << 1)
                | csdbuf.v1.c_size_mult_low;

        return (uint32_t) (c_size + 1) << (c_size_mult + read_bl_len - 7);
    } else if (csdbuf.v2.csd_ver == 1) {
        uint32_t c_size = ((uint32_t) csdbuf.v2.c_size_high << 16)
                | (csdbuf.v2.c_size_mid << 8) | csdbuf.v2.c_size_low;

        return (c_size + 1) << 10;
    } else {
        return 0;
    }
}
#endif

bool BBSD_read_block(BBSDCard *sd, uint32_t block, uint8_t *buffer) {
#ifndef SD_FASTER
    if (!sd->initialized) {
        return false;
    }
#endif
    bool result = false;

    uint32_t addressable_block;

    if (sd->type == BBSD_CARD_TYPE_SDHC) {
        // SDHC is addressed by block number
        addressable_block = block;
    } else {
        // Other cards use absolute addressing
        addressable_block = block << 9;
    }

    if (BBSD_command(sd, 17, addressable_block) || !wait_for_block_start(sd->spi, 10)) {
        goto finally;
    }

    // Read data into buffer
    for (uint16_t i = 0; i < 512; i++) {
        *buffer++ = BBSPI_recv_byte(sd->spi);
    }

    // Get checksum too (and ignore it ;) )
    BBSPI_recv_byte(sd->spi);
    BBSPI_recv_byte(sd->spi);

    result = true;

finally:
    BBSPI_deassert_cs(sd->spi);
    return result;
}

#ifndef SD_BLOCK_READ_ONLY
bool BBSD_read_data(BBSDCard *sd, uint32_t block, uint16_t start_ofs, uint16_t count, uint8_t *buffer) {
    // Do args make sense?
#ifndef SD_FASTER
    if (!sd->initialized || (start_ofs + count) > 512) {
        return false;
    }
#endif

    // We've already read 0 bytes :D
    if (count == 0) {
        return true;
    }

    bool result = false;

    // Do we need to re-address the card?
    if (!sd->have_current_block                             // Yes, if we're not currently reading a block, or
            || block != sd->current_block_start             // .. they don't want data from the current block, or
            || start_ofs < sd->current_block_offset) {      // .. they want data from before where we currently are.

        uint32_t addressable_block;
        if (sd->type == BBSD_CARD_TYPE_SDHC) {
            // SDHC is addressed by block number
            addressable_block = block;
        } else {
            // Other cards use absolute addressing
            addressable_block = block << 9;
        }

        if (BBSD_command(sd, 17, addressable_block) || !wait_for_block_start(sd->spi, 10)) {
            goto finally;
        }

        sd->have_current_block = true;
        sd->current_block_start = block;
        sd->current_block_offset = 0;
    }

    // Skip data before offset
    for (; sd->current_block_offset < start_ofs; sd->current_block_offset++) {
        BBSPI_recv_byte(sd->spi);
    }

    // Read data into buffer
    for (uint16_t i = 0; i < count; i++) {
        *buffer++ = BBSPI_recv_byte(sd->spi);
    }

    sd->current_block_offset += count;

    // Finish block if partial read isn't supported
#ifndef SD_UNSAFE_PARTIAL_READ
    if (!sd->can_partial_read) {
        // TODO this isn't supporting the case where partial read has crossed a block boundary! look into that!
        while (sd->current_block_offset++ < 513) {
            BBSPI_recv_byte(sd->spi);
        }

        // Get checksum too (and ignore it ;) )
        BBSPI_recv_byte(sd->spi);
        BBSPI_recv_byte(sd->spi);
    }
#endif

    result = true;

finally:
    BBSPI_deassert_cs(sd->spi);
    return result;
}
#endif

/* ********* PRIVATE *********** */
static bool wait_for_card(BBSPI *spi, uint32_t nops) {
    for (uint32_t i = 0; i < nops; i++) {
        if (BBSPI_recv_byte(spi) == 0xFF) {
            return true;
        }
    }
    return false;
}

static void reset_card(BBSPI *spi) {
    BBSPI_deassert_cs(spi);

    for (int i = 0; i < 10; i++) {
        BBSPI_recv_byte(spi);
    }
}

static bool wait_for_block_start(BBSPI *spi, uint32_t nops) {
    for (uint32_t i = 0; i < nops; i++) {
        uint8_t status = BBSPI_recv_byte(spi);
        if (status != 0xFF) {
            if (status == BLOCK_START) {
                return true;
            } else {
                // something happened, but not what we expected :D
                return false;
            }
        }
    }

    return false;
}

static bool send_idle(BBSPI *spi) {
    for (int i = 0; i < MAX_IDLE_TRIES; i++) {
        if (raw_sd_command(spi, 0, 0) == R1_IDLE_STATE) {
            return true;
        }
    }

    return false;
}

static BBSDCardType get_card_type(BBSPI *spi) {
    // Let's try a CMD8...
    if (raw_sd_command(spi, 8, 0x1AA) & R1_ILLEGAL_COMMAND) {
        return BBSD_CARD_TYPE_V1;
    } else {
        // Ignore all but last byte...
        BBSPI_recv_byte(spi);
        BBSPI_recv_byte(spi);
        BBSPI_recv_byte(spi);
        BBSPI_recv_byte(spi);
        uint8_t result = BBSPI_recv_byte(spi);

        if (result == 0xAA) {
            return BBSD_CARD_TYPE_UNKNOWN;
        } else {
            return BBSD_CARD_TYPE_V2;
        }
    }
}

static bool try_acmd41(BBSPI *spi, uint32_t nops, uint32_t supports) {
    for (uint32_t i = 0; i < nops; i++) {
        if (raw_sd_acommand(spi, 41, supports) == R1_READY_STATE) {
            return true;
        }
    }

    return false;
}

static uint8_t raw_sd_command(BBSPI *spi, uint8_t command, uint32_t arg) {
    BBSPI_assert_cs(spi);

    if (!wait_for_card(spi, 1000)) {
        return 0xFF;
    }

    BBSPI_send_byte(spi, command | 0x40);
    for (int8_t s = 24; s >= 0; s -= 8)
        BBSPI_send_byte(spi, arg >> s);

    uint8_t crc = 0xFF;
    if (command == 0)
        crc = 0x95;
    if (command == 8)
        crc = 0x87;
    BBSPI_send_byte(spi, crc);

    uint8_t result = 0xFF;
    for (uint8_t i = 0; ((result = BBSPI_recv_byte(spi)) & 0x80) && i != 0xFF;
            i++)
        ;
    return result;
}

static uint8_t raw_sd_acommand(BBSPI *spi, uint8_t command, uint32_t arg) {
    raw_sd_command(spi, 55, 0);
    return raw_sd_command(spi, command, arg);
}

#ifndef SD_BLOCK_READ_ONLY
static bool sd_partial_read_p(BBSDCard *sd) {
    if (!BBSD_get_csd(sd, &csdbuf)) {
        return 0;
    }
    if (csdbuf.v1.csd_ver == 0) {
        return csdbuf.v1.read_bl_partial;
    } else if (csdbuf.v2.csd_ver == 1) {
        return csdbuf.v2.read_bl_partial;
    } else {
        return false;
    }
}
#endif

/* Handlers for block device functions */
static uint32_t sd_device_block_size_func(BlockDevice *device) {
    return 512;
}

static bool sd_device_read_block_func(BlockDevice *device, uint32_t block, void *buffer) {
#ifndef SD_FASTER
    if (!device->initialized) {
        return false;
    } else {
#endif
        // TODO bounds check start_ofs!
        return BBSD_read_block(device->device_data, block, buffer);
#ifndef SD_FASTER
    }
#endif
}

static bool sd_device_read_func(BlockDevice *device, uint32_t block, uint32_t start_ofs, uint32_t len, void *buffer) {
#ifndef SD_BLOCK_READ_ONLY
#  ifndef SD_FASTER
    if (!device->initialized) {
        return false;
    } else {
#  endif
        // TODO bounds check start_ofs!
        return BBSD_read_data(device->device_data, block, start_ofs & 0xFFFF, len, buffer);
#   ifndef SD_FASTER
    }
#  endif
#else
    return false;
#endif
}

static bool sd_device_write_func(BlockDevice *device, uint32_t block, uint32_t start_ofs, uint32_t len, void *buffer) {
    // Not yet implemented
    return false;
}
