rosco-m68k/rosco_m68k/code/firmware/rosco_m68k_firmware/rosco_m68k_private.asm

;------------------------------------------------------------
;                                  ___ ___ _
;  ___ ___ ___ ___ ___       _____|  _| . | |_
; |  _| . |_ -|  _| . |     |     | . | . | '_|
; |_| |___|___|___|___|_____|_|_|_|___|___|_,_|
;                     |_____|       firmware v2
;------------------------------------------------------------
; Copyright (c)2019-2022 Ross Bamford and contributors
; See top-level LICENSE.md for licence information.
;
; Global equates for firmware code
;------------------------------------------------------------

; Version (embedded into firmware at 0xFC0400)
; MSW is flags, LSW is split into major (MSB) and minor (LSB)
;
; Flags:
; bit 0 - 12: Reserved
; bit 13    : Flashable ROM (i.e. HUGEROM).
; bit 14    : Requires larger system data area
; bit 15    : Snapshot version
  ifd HUGEROM
RELEASE_VER     equ     $60000220
  else
RELEASE_VER     equ     $40000220
  endif

VECTORS_LOAD    equ     $00000000

; Bits we use in the firmware reserved area (non-BSS).
BERR_SAVED      equ     $1180       ; N.B. Duplicated in machine.h - must be kept in sync
BERR_FLAG       equ     $1184       ; N.B. Duplicated in machine.h - must be kept in sync

; Initialisation
INIT_SSP    equ     RAMLIMIT
