rosco-m68k/rosco_m68k/code/firmware/rosco_m68k_firmware/stage2/idehdd/include/part.h

/*
 * vim: set et ts=4 sw=4
 *------------------------------------------------------------
 *                                  ___ ___ _
 *  ___ ___ ___ ___ ___       _____|  _| . | |_
 * |  _| . |_ -|  _| . |     |     | . | . | '_|
 * |_| |___|___|___|___|_____|_|_|_|___|___|_,_|
 *                     |_____|       firmware v2
 * ------------------------------------------------------------
 * Copyright (c) 2021 Ross Bamford & Contributors
 * MIT License
 *
 * Partition access structs and routines (readonly, for firmware)
 * (Only MBR is supported yet, GPT maybe TODO).
 * ------------------------------------------------------------
 */
#ifndef __ROSCO_M68K_PART_H
#define __ROSCO_M68K_PART_H

#include <stdint.h>
#include <stdbool.h>
#include <ata.h>
#include "part_mbr.h"

typedef enum {
    PART_INIT_OK,
    PART_INIT_READ_FAILURE,
    PART_INIT_BAD_SIGNATURE,
    PART_INIT_GENERAL_FAILURE
} PartInitStatus;

typedef struct {
    uint8_t     status;
    uint8_t     type;
    uint32_t    lba_start;
    uint32_t    sector_count;
} RuntimePart;

typedef struct {
    ATADevice   *device;
    RuntimePart parts[4];
} PartHandle;

PartInitStatus Part_init(PartHandle *handle, ATADevice *device);
uint32_t Part_read(PartHandle *handle, uint8_t part_num, uint8_t *buffer, uint32_t start, uint32_t count);
bool Part_valid(PartHandle *handle, uint8_t part);

#endif//__ROSCO_M68K_PART_H
